kateya-luo/luoye/firmware/docs/UI154_23_CHAPTER_SUMMARY_PREVIEW.png

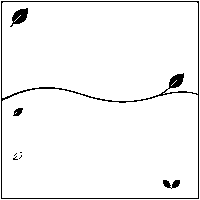
firmware/docs/UI154_23_CHAPTER_SUMMARY_PREVIEW.png
