kateya-luo/luoye/firmware/docs/UI154_23_CHAPTER_SUMMARY_TEXT_PREVIEW.png

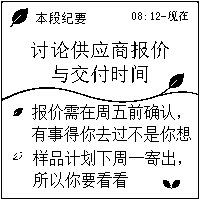
firmware/docs/UI154_23_CHAPTER_SUMMARY_TEXT_PREVIEW.png
