kateya-luo/luoye/firmware/docs/UI154_23PAGES_BW_FAST_PREVIEW.png

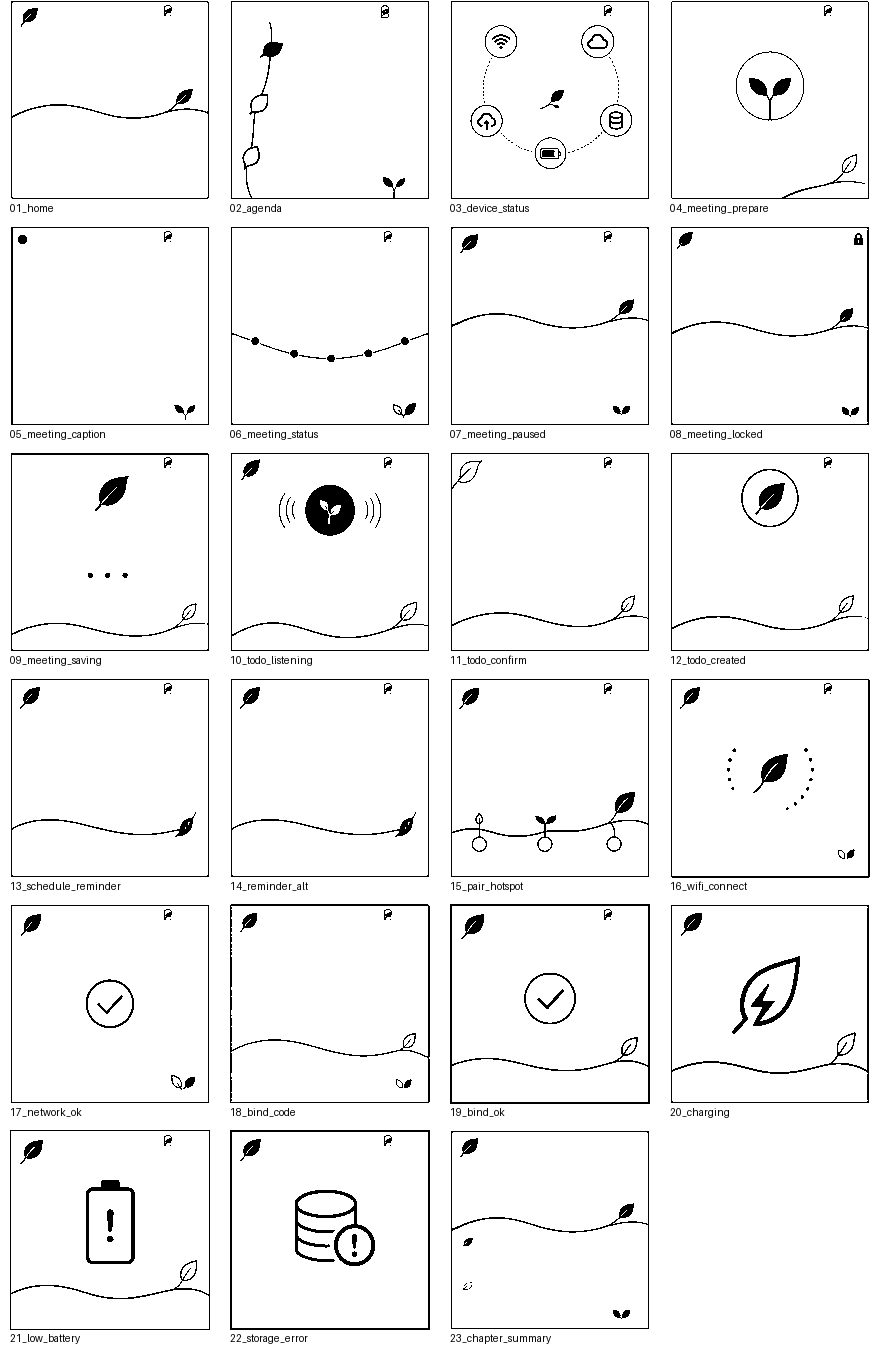
firmware/docs/UI154_23PAGES_BW_FAST_PREVIEW.png
