kateya-luo/luoye/firmware/docs/UI154_FIRMWARE_LIGHT96_FONT_PREVIEW.png

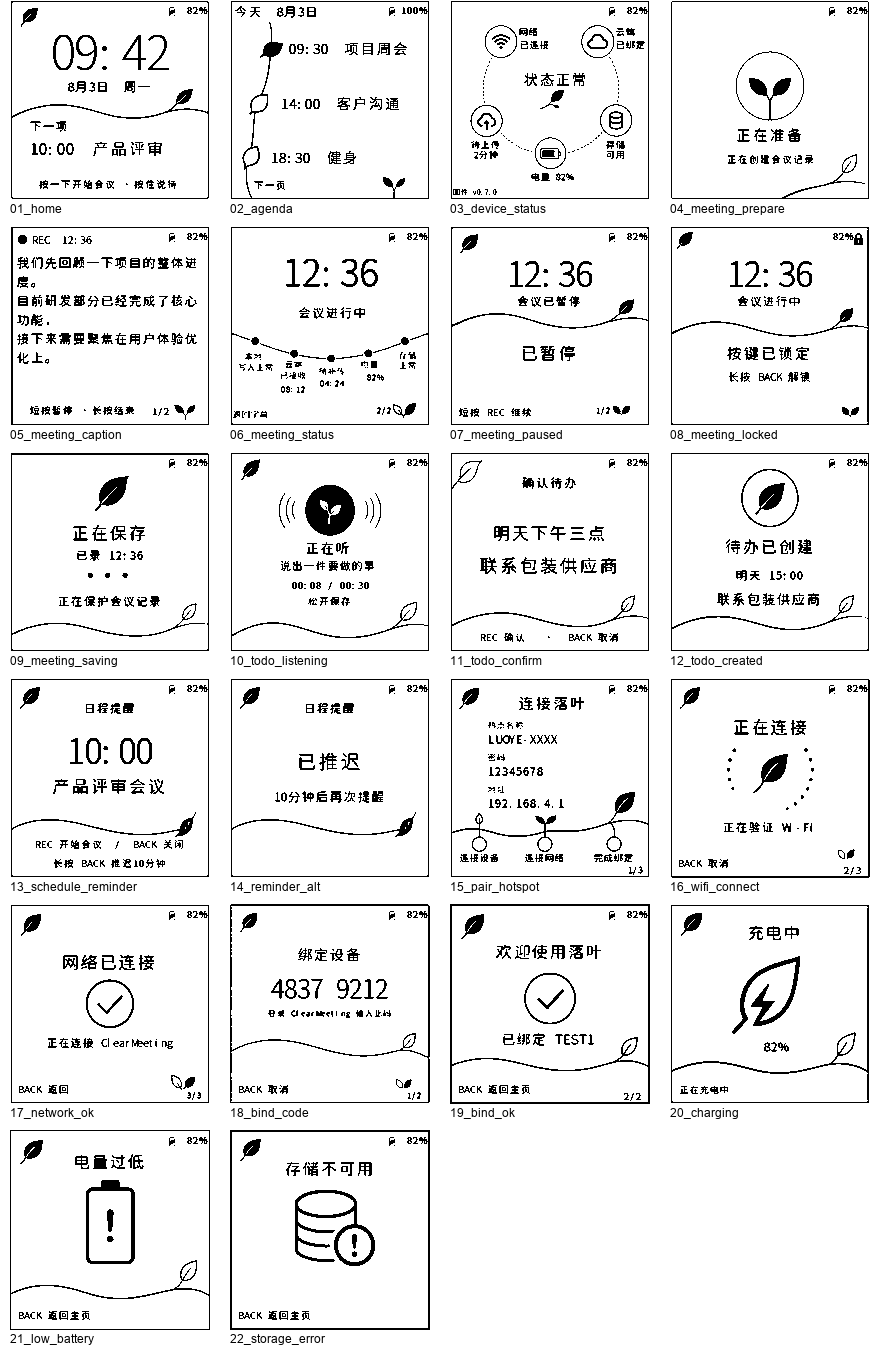
firmware/docs/UI154_FIRMWARE_LIGHT96_FONT_PREVIEW.png
