kateya-luo/luoye/firmware/docs/ui154_firmware_r2_pages/01_home.png

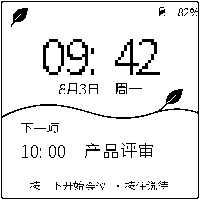
firmware/docs/ui154_firmware_r2_pages/01_home.png
