kateya-luo/luoye/firmware/docs/ui154_firmware_r2_pages/03_device_status.png

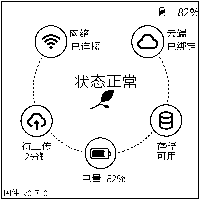
firmware/docs/ui154_firmware_r2_pages/03_device_status.png
