kateya-luo/luoye/firmware/docs/ui154_firmware_r2_pages/04_meeting_prepare.png

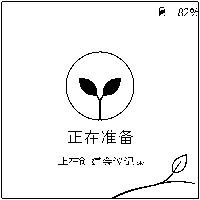
firmware/docs/ui154_firmware_r2_pages/04_meeting_prepare.png
