kateya-luo/luoye/firmware/docs/ui154_firmware_r2_pages/05_meeting_caption.png

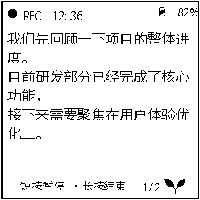
firmware/docs/ui154_firmware_r2_pages/05_meeting_caption.png
