kateya-luo/luoye/firmware/docs/ui154_firmware_r2_pages/06_meeting_status.png

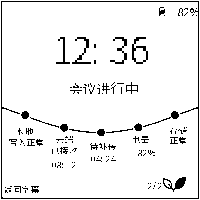
firmware/docs/ui154_firmware_r2_pages/06_meeting_status.png
