kateya-luo/luoye/firmware/docs/ui154_firmware_r2_pages/07_meeting_paused.png

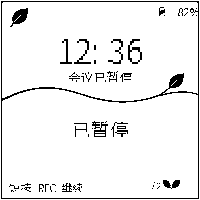
firmware/docs/ui154_firmware_r2_pages/07_meeting_paused.png
