kateya-luo/luoye/firmware/docs/ui154_firmware_r2_pages/08_meeting_locked.png

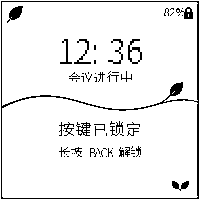
firmware/docs/ui154_firmware_r2_pages/08_meeting_locked.png
