kateya-luo/luoye/firmware/docs/ui154_firmware_r2_pages/09_meeting_saving.png

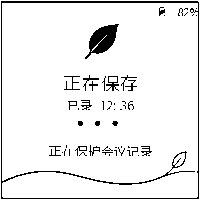
firmware/docs/ui154_firmware_r2_pages/09_meeting_saving.png
