kateya-luo/luoye/firmware/docs/ui154_firmware_r2_pages/13_schedule_reminder.png

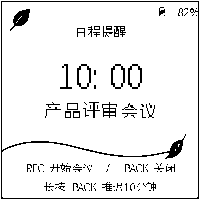
firmware/docs/ui154_firmware_r2_pages/13_schedule_reminder.png
