kateya-luo/luoye/firmware/docs/ui154_firmware_r2_pages/14_reminder_alt.png

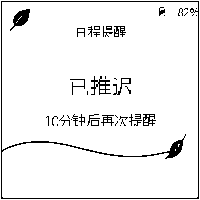
firmware/docs/ui154_firmware_r2_pages/14_reminder_alt.png
