kateya-luo/luoye/firmware/docs/ui154_firmware_r2_pages/15_pair_hotspot.png

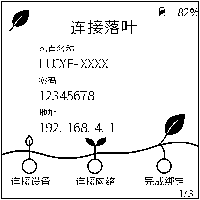
firmware/docs/ui154_firmware_r2_pages/15_pair_hotspot.png
