kateya-luo/luoye/firmware/docs/ui154_firmware_r2_pages/16_wifi_connect.png

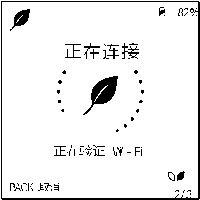
firmware/docs/ui154_firmware_r2_pages/16_wifi_connect.png
