kateya-luo/luoye/firmware/docs/ui154_firmware_r2_pages/17_network_ok.png

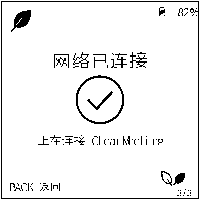
firmware/docs/ui154_firmware_r2_pages/17_network_ok.png
