kateya-luo/luoye/firmware/docs/ui154_firmware_r2_pages/20_charging.png

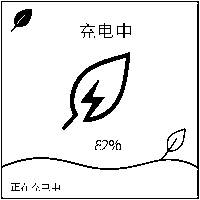
firmware/docs/ui154_firmware_r2_pages/20_charging.png
