kateya-luo/luoye/firmware/docs/ui154_firmware_r2_pages/21_low_battery.png

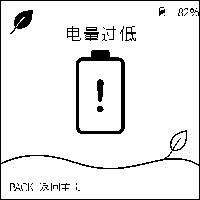
firmware/docs/ui154_firmware_r2_pages/21_low_battery.png
