kateya-luo/luoye/firmware/docs/ui154_firmware_r2_pages/22_storage_error.png

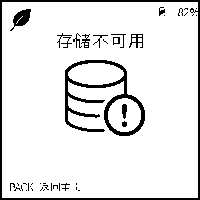
firmware/docs/ui154_firmware_r2_pages/22_storage_error.png
