kateya-luo/luoye/firmware/docs/UI154_FIRMWARE_R2_PREVIEW.png

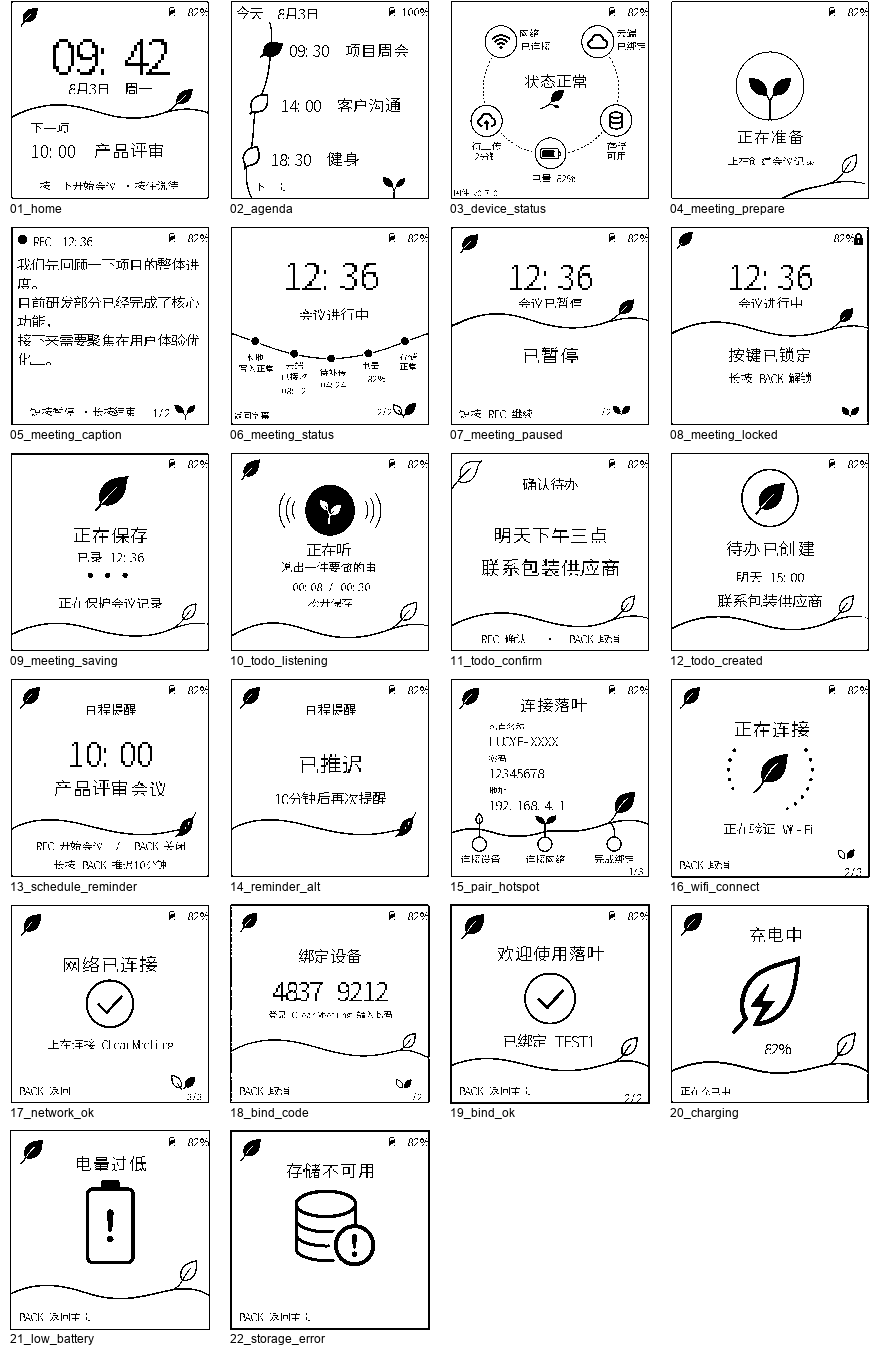
firmware/docs/UI154_FIRMWARE_R2_PREVIEW.png
