kateya-luo/luoye/firmware/docs/UI154_FIRMWARE_REGULAR_NATIVE_PREVIEW.png

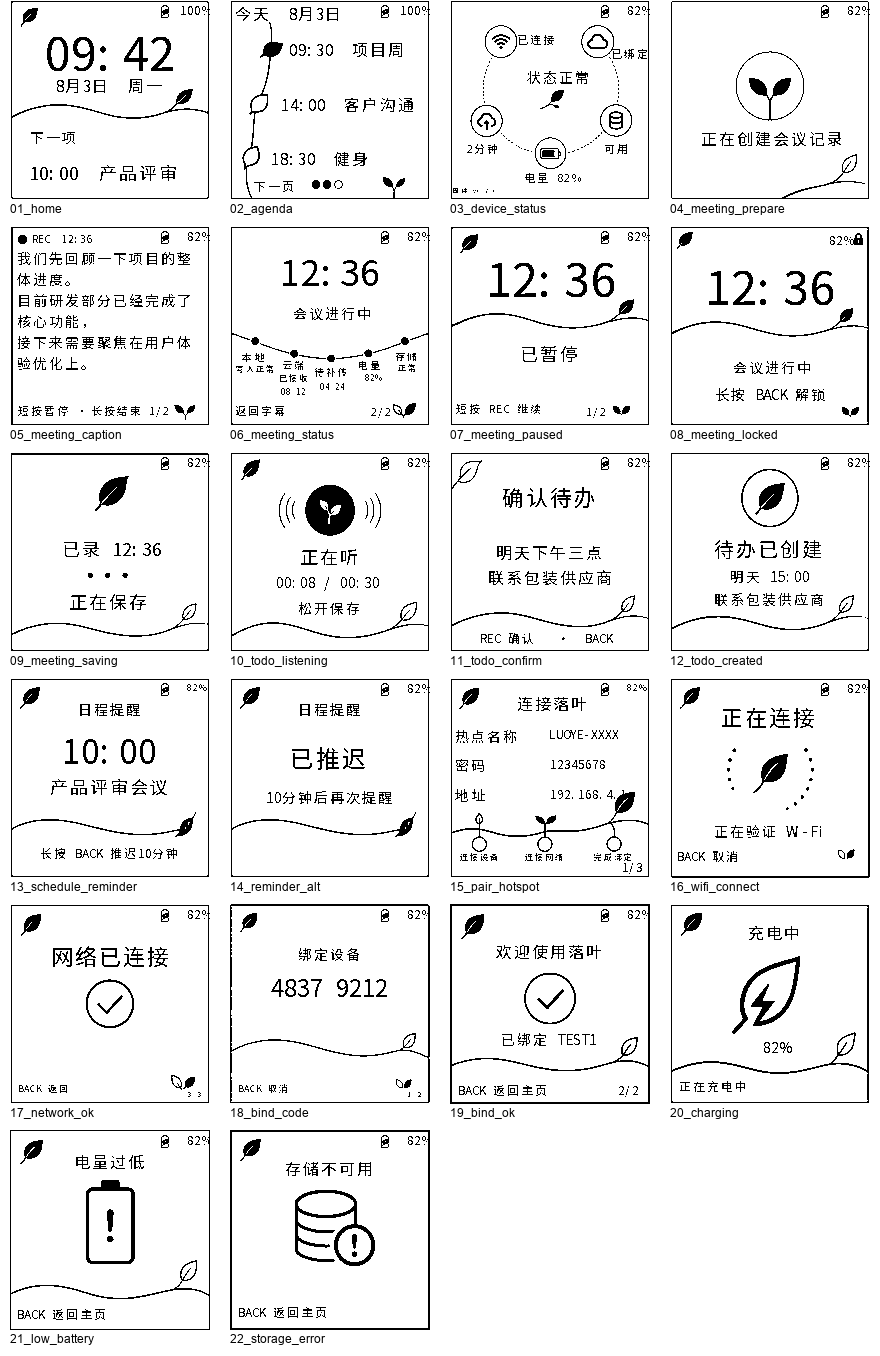
firmware/docs/UI154_FIRMWARE_REGULAR_NATIVE_PREVIEW.png
