kateya-luo/luoye/firmware/docs/UI154_FIRMWARE_SIMSUN_BW_FAST_PREVIEW.png

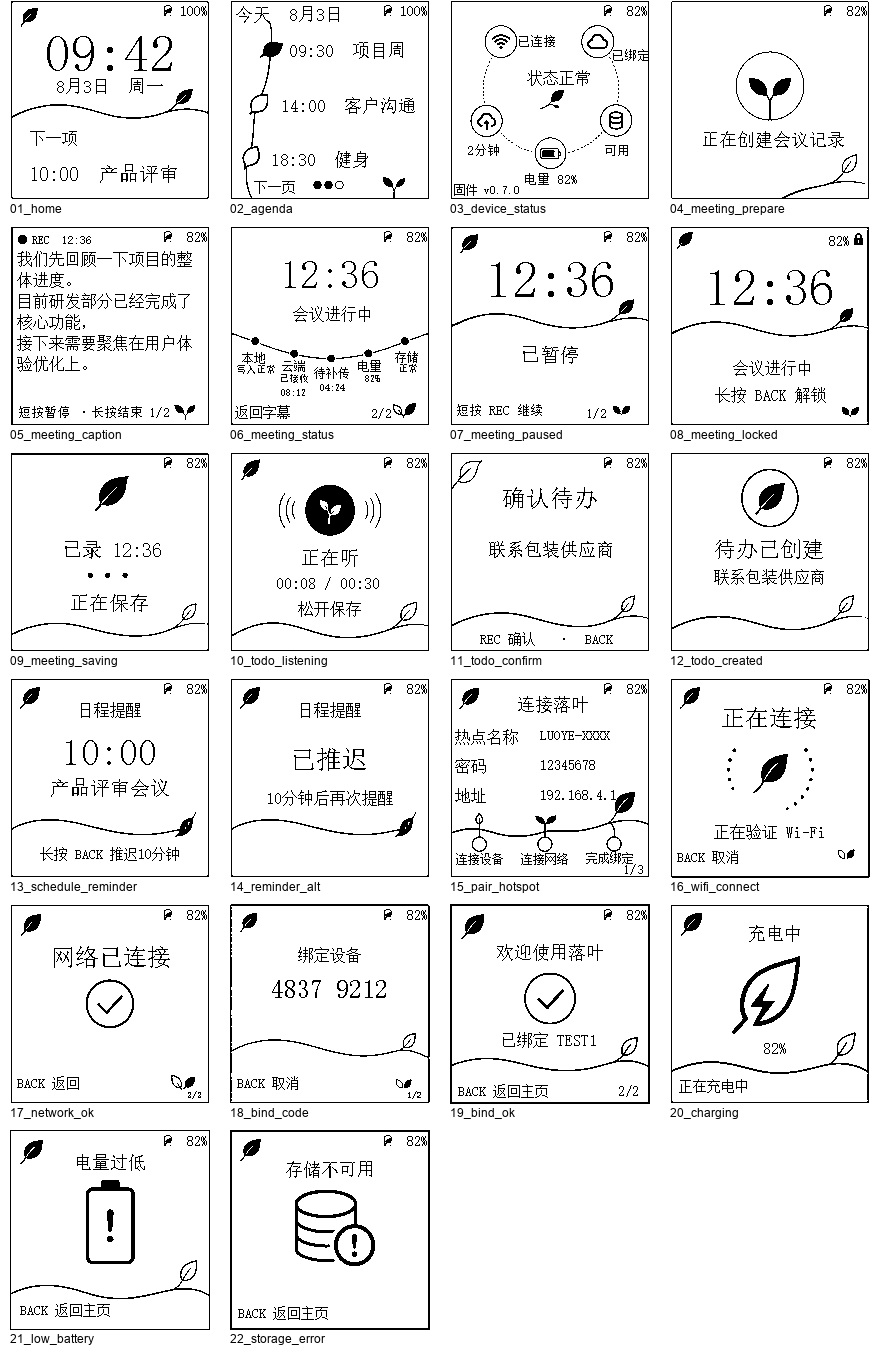
firmware/docs/UI154_FIRMWARE_SIMSUN_BW_FAST_PREVIEW.png
