kateya-luo/luoye/firmware/docs/UI154_FIRMWARE_SIMSUN_GRAY4_PREVIEW.png

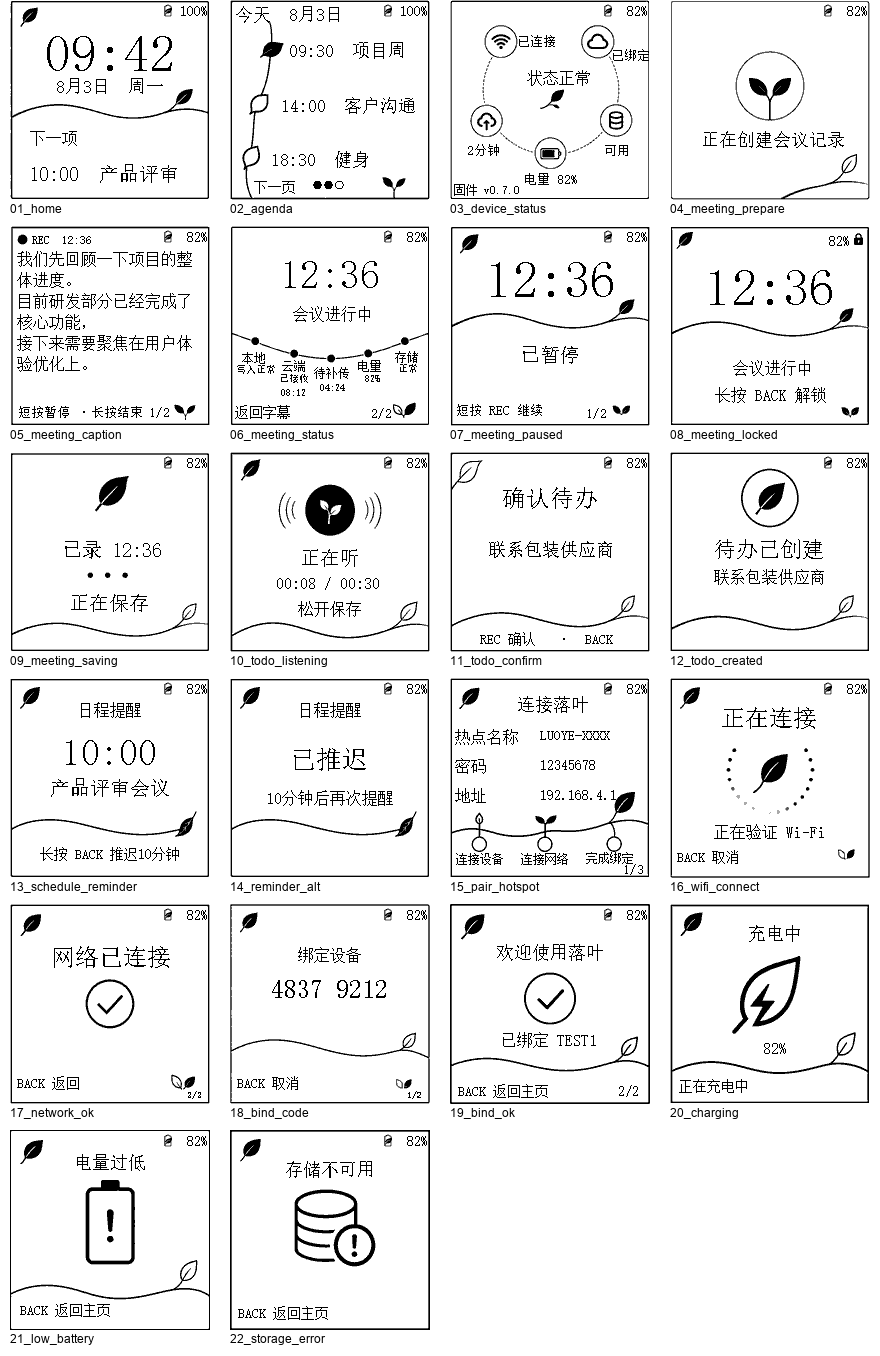
firmware/docs/UI154_FIRMWARE_SIMSUN_GRAY4_PREVIEW.png
