kateya-luo/luoye/firmware/docs/ui154_native_font_pages/01_home.png

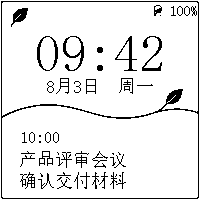
firmware/docs/ui154_native_font_pages/01_home.png
