kateya-luo/luoye/firmware/docs/ui154_native_font_pages/02_agenda.png

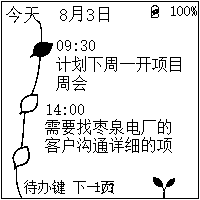
firmware/docs/ui154_native_font_pages/02_agenda.png
