kateya-luo/luoye/firmware/docs/ui154_native_font_pages/04_meeting_prepare.png

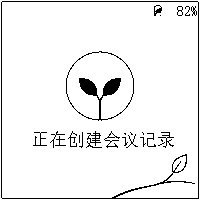
firmware/docs/ui154_native_font_pages/04_meeting_prepare.png
