kateya-luo/luoye/firmware/docs/ui154_native_font_pages/05_meeting_caption.png

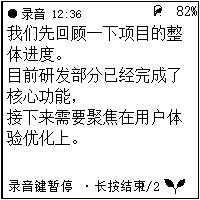
firmware/docs/ui154_native_font_pages/05_meeting_caption.png
