kateya-luo/luoye/firmware/docs/ui154_native_font_pages/07_meeting_paused.png

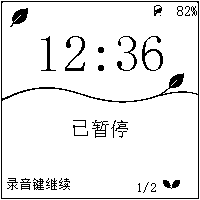
firmware/docs/ui154_native_font_pages/07_meeting_paused.png
