kateya-luo/luoye/firmware/docs/ui154_native_font_pages/08_meeting_locked.png

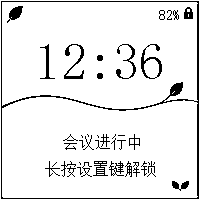
firmware/docs/ui154_native_font_pages/08_meeting_locked.png
