kateya-luo/luoye/firmware/docs/ui154_native_font_pages/09_meeting_saving.png

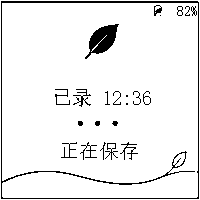
firmware/docs/ui154_native_font_pages/09_meeting_saving.png
