kateya-luo/luoye/firmware/docs/ui154_native_font_pages/13_schedule_reminder.png

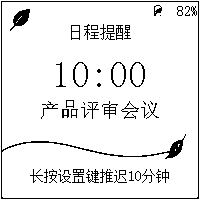
firmware/docs/ui154_native_font_pages/13_schedule_reminder.png
