kateya-luo/luoye/firmware/docs/ui154_native_font_pages/14_reminder_alt.png

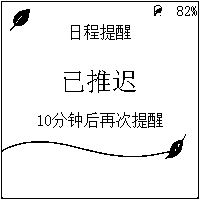
firmware/docs/ui154_native_font_pages/14_reminder_alt.png
