kateya-luo/luoye/firmware/docs/ui154_native_font_pages/15_pair_hotspot.png

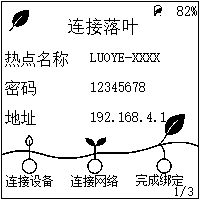
firmware/docs/ui154_native_font_pages/15_pair_hotspot.png
