kateya-luo/luoye/firmware/docs/ui154_native_font_pages/16_wifi_connect.png

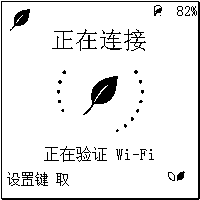
firmware/docs/ui154_native_font_pages/16_wifi_connect.png
