kateya-luo/luoye/firmware/docs/ui154_native_font_pages/18_bind_code.png

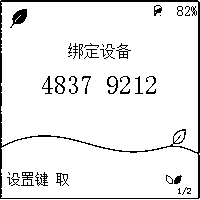
firmware/docs/ui154_native_font_pages/18_bind_code.png
