kateya-luo/luoye/firmware/docs/ui154_native_font_pages/19_bind_ok.png

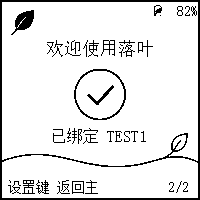
firmware/docs/ui154_native_font_pages/19_bind_ok.png
