kateya-luo/luoye/firmware/docs/ui154_native_font_pages/20_charging.png

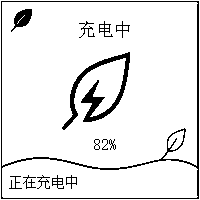
firmware/docs/ui154_native_font_pages/20_charging.png
