kateya-luo/luoye/firmware/docs/ui154_native_font_pages/21_low_battery.png

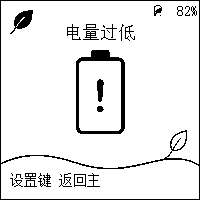
firmware/docs/ui154_native_font_pages/21_low_battery.png
