kateya-luo/luoye/firmware/docs/ui154_native_font_pages/22_storage_error.png

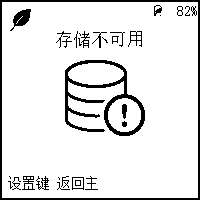
firmware/docs/ui154_native_font_pages/22_storage_error.png
