kateya-luo/luoye/firmware/docs/UI154_THRESHOLD_112.png

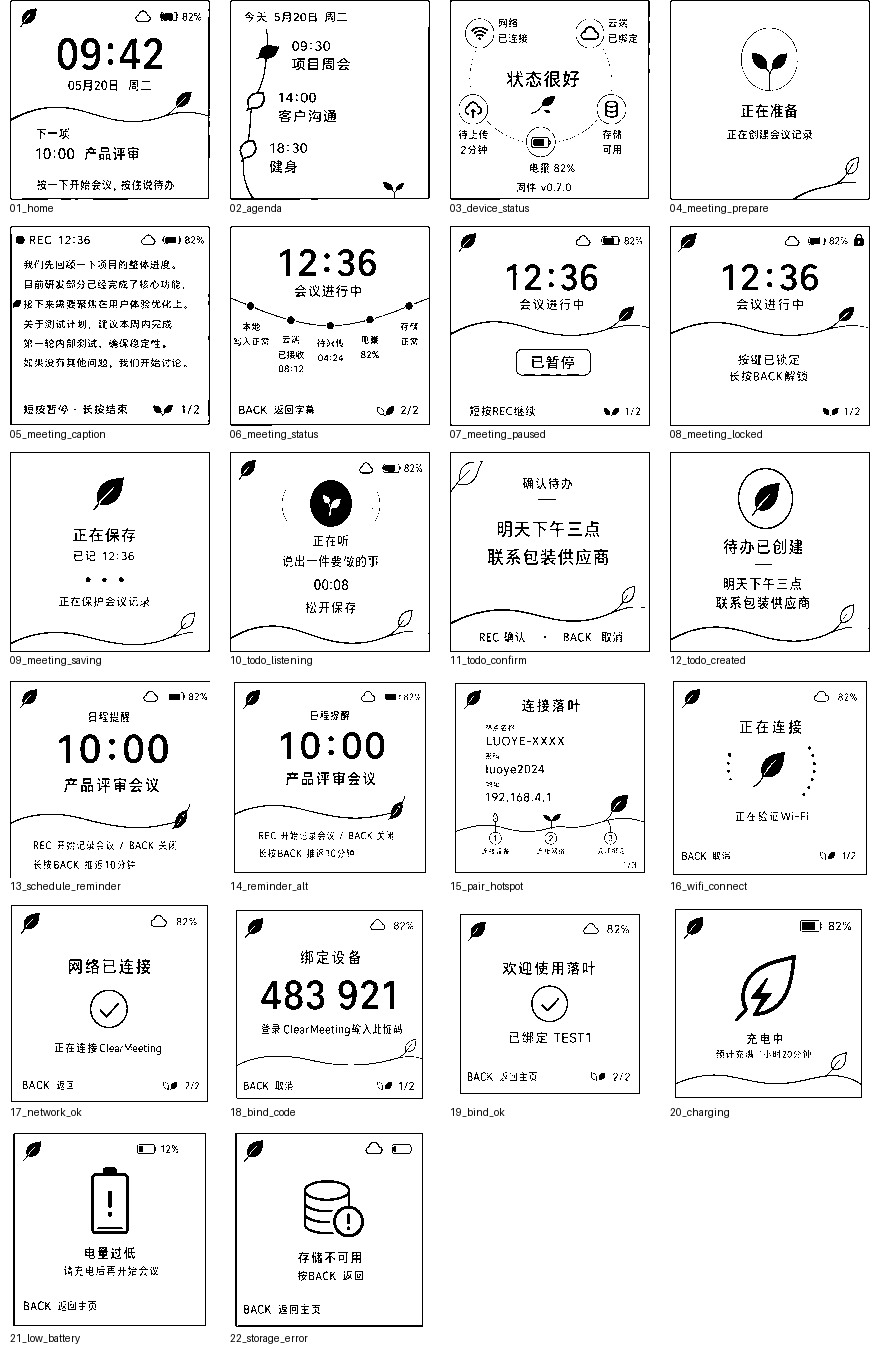
firmware/docs/UI154_THRESHOLD_112.png
