kateya-luo/luoye/firmware/docs/UI154_THRESHOLD_192.png

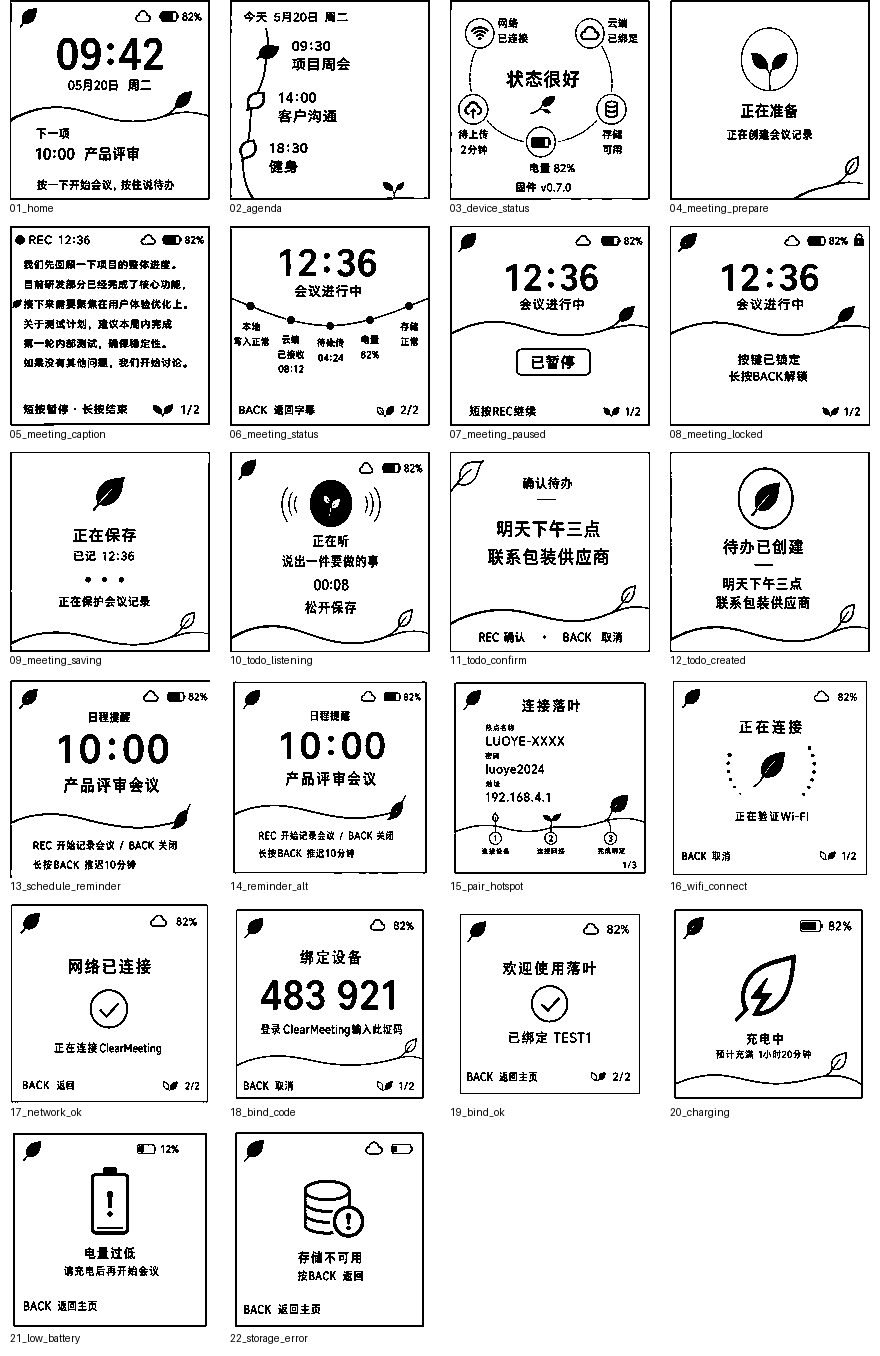
firmware/docs/UI154_THRESHOLD_192.png
