kateya-luo/luoye/firmware/docs/ui154_firmware_r2_pages/10_todo_listening.png

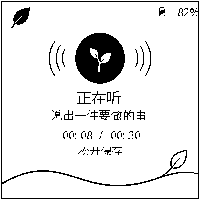
firmware/docs/ui154_firmware_r2_pages/10_todo_listening.png
