kateya-luo/luoye/firmware/docs/ui154_firmware_r2_pages/11_todo_confirm.png

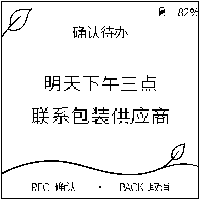
firmware/docs/ui154_firmware_r2_pages/11_todo_confirm.png
