kateya-luo/luoye/firmware/docs/ui154_firmware_r2_pages/12_todo_created.png

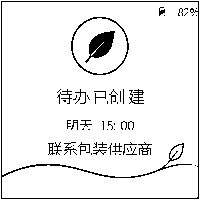
firmware/docs/ui154_firmware_r2_pages/12_todo_created.png
