kateya-luo/luoye/firmware/docs/ui154_native_font_pages/11_todo_confirm.png

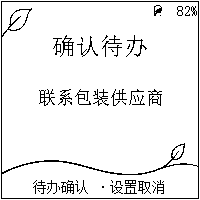
firmware/docs/ui154_native_font_pages/11_todo_confirm.png
