kateya-luo/luoye/firmware/docs/ui154_native_font_pages/12_todo_created.png

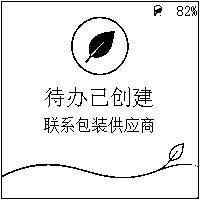
firmware/docs/ui154_native_font_pages/12_todo_created.png
