kateya-luo/luoye/firmware/main/ui_render.c

// Luoye 1.54-inch UI renderer: approved 200x200 artwork + live data overlays.
#include "ui_render.h"
#include "ui_font.h"
#include "luoye_build_info.h"
#include "net_uploader.h"
#include "agenda_todo.h"
#include "epd_ssd1681.h"
#include "ui154_layout_generated.h"

#include <stdio.h>
#include <string.h>
#include <time.h>
#include "esp_log.h"
#include "esp_timer.h"
#include "freertos/FreeRTOS.h"
#include "freertos/semphr.h"
#include "freertos/task.h"

#define DEFAULT_UI_TIMEZONE_OFFSET_MINUTES 480
/* SSD1681 can miss a tiny glyph-only auto-diff after panel sleep.  Keep one
   stable, proven-size window for both dynamic home fields instead: battery
   (158,4,40,17) and clock (27,27,147,52). */
#define HOME_CLOCK_BATTERY_X 24
#define HOME_CLOCK_BATTERY_Y 2
#define HOME_CLOCK_BATTERY_WIDTH 174
#define HOME_CLOCK_BATTERY_HEIGHT 78

static const char *TAG = "ui154";
static uint8_t s_fb[EPD_FB_BYTES];              // packed 1bpp: 0=white, 1=black
static SemaphoreHandle_t s_lock;
static TaskHandle_t s_task;
static volatile int s_pending = -1;
static volatile bool s_busy;
static bool s_assets_ready;
static bool s_have_panel_screen;
static uint32_t s_panel_screen;

/* Stable identity of the visual page, intentionally excluding values that can
   change inside the same page (clock, battery, network and upload status).
   This is the final guard against an asynchronous partial request painting a
   different page over the previous panel image. */
static uint32_t screen_identity(const app_state_t *state) {
  if (!state) return 0;
  if (state->overlay != APP_OV_NONE) {
    return 0x10000U | (uint32_t)state->overlay;
  }
  switch (state->mode) {
    case APP_MODE_STANDBY:
      if (state->page == 0 && state->charging != APP_CHG_NONE) return 0x20010U;
      if (state->page == 1) {
        return 0x20020U | ((uint32_t)state->agenda_page << 8);
      }
      if (state->page == 2) return 0x20030U;
      return 0x20000U;
    case APP_MODE_STARTING: return 0x30000U;
    case APP_MODE_RECORDING:
      if (state->locked) return 0x40010U;
      if (state->paused) return 0x40020U;
      if ((state->page & 1U) != 0) return 0x40030U;
      return 0x40000U;
    case APP_MODE_CLOSING: return 0x50000U;
    case APP_MODE_ENDING: return 0x50010U;
    case APP_MODE_STORAGE_ERROR:
      return 0x60000U | (uint32_t)state->error;
    case APP_MODE_PAIRING:
      return 0x70000U | (uint32_t)state->pairing;
    case APP_MODE_OFF: return 0x80000U;
    default: return 0x90000U | (uint32_t)state->mode;
  }
}

static bool home_clock_active(const app_state_t *state) {
  return state && state->mode == APP_MODE_STANDBY &&
         state->overlay == APP_OV_NONE && state->page == 0 &&
         state->charging == APP_CHG_NONE;
}

static int64_t ui_clock_seconds(void) {
  time_t now = time(NULL);
  int64_t monotonic_ms = esp_timer_get_time() / 1000;
  return now >= 1577836800 ? (int64_t)now : monotonic_ms / 1000;
}

// 5x7 ASCII for compact status fields and a usable fallback when font16.bin is absent.
static const uint8_t FONT[59][5] = {
  {0x00,0x00,0x00,0x00,0x00},{0x00,0x00,0x5F,0x00,0x00},{0x00,0x07,0x00,0x07,0x00},
  {0x14,0x7F,0x14,0x7F,0x14},{0x24,0x2A,0x7F,0x2A,0x12},{0x23,0x13,0x08,0x64,0x62},
  {0x36,0x49,0x55,0x22,0x50},{0x00,0x05,0x03,0x00,0x00},{0x00,0x1C,0x22,0x41,0x00},
  {0x00,0x41,0x22,0x1C,0x00},{0x14,0x08,0x3E,0x08,0x14},{0x08,0x08,0x3E,0x08,0x08},
  {0x00,0x50,0x30,0x00,0x00},{0x08,0x08,0x08,0x08,0x08},{0x00,0x60,0x60,0x00,0x00},
  {0x20,0x10,0x08,0x04,0x02},{0x3E,0x51,0x49,0x45,0x3E},{0x00,0x42,0x7F,0x40,0x00},
  {0x42,0x61,0x51,0x49,0x46},{0x21,0x41,0x45,0x4B,0x31},{0x18,0x14,0x12,0x7F,0x10},
  {0x27,0x45,0x45,0x45,0x39},{0x3C,0x4A,0x49,0x49,0x30},{0x01,0x71,0x09,0x05,0x03},
  {0x36,0x49,0x49,0x49,0x36},{0x06,0x49,0x49,0x29,0x1E},{0x00,0x36,0x36,0x00,0x00},
  {0x00,0x56,0x36,0x00,0x00},{0x08,0x14,0x22,0x41,0x00},{0x14,0x14,0x14,0x14,0x14},
  {0x00,0x41,0x22,0x14,0x08},{0x02,0x01,0x51,0x09,0x06},{0x32,0x49,0x79,0x41,0x3E},
  {0x7E,0x11,0x11,0x11,0x7E},{0x7F,0x49,0x49,0x49,0x36},{0x3E,0x41,0x41,0x41,0x22},
  {0x7F,0x41,0x41,0x22,0x1C},{0x7F,0x49,0x49,0x49,0x41},{0x7F,0x09,0x09,0x09,0x01},
  {0x3E,0x41,0x49,0x49,0x7A},{0x7F,0x08,0x08,0x08,0x7F},{0x00,0x41,0x7F,0x41,0x00},
  {0x20,0x40,0x41,0x3F,0x01},{0x7F,0x08,0x14,0x22,0x41},{0x7F,0x40,0x40,0x40,0x40},
  {0x7F,0x02,0x0C,0x02,0x7F},{0x7F,0x04,0x08,0x10,0x7F},{0x3E,0x41,0x41,0x41,0x3E},
  {0x7F,0x09,0x09,0x09,0x06},{0x3E,0x41,0x51,0x21,0x5E},{0x7F,0x09,0x19,0x29,0x46},
  {0x46,0x49,0x49,0x49,0x31},{0x01,0x01,0x7F,0x01,0x01},{0x3F,0x40,0x40,0x40,0x3F},
  {0x1F,0x20,0x40,0x20,0x1F},{0x3F,0x40,0x38,0x40,0x3F},{0x63,0x14,0x08,0x14,0x63},
  {0x07,0x08,0x70,0x08,0x07},{0x61,0x51,0x49,0x45,0x43},
};

void ui_fb_rect(int x, int y, int w, int h) {
  for (int py = y; py < y + h; py++) {
    if (py < 0 || py >= EPD_LANDSCAPE_H) continue;
    for (int px = x; px < x + w; px++) {
      if (px < 0 || px >= EPD_LANDSCAPE_W) continue;
      size_t index = py * EPD_FB_STRIDE + (px >> 3);
      s_fb[index] |= (uint8_t)(0x80U >> (px & 7));
    }
  }
}

static void white_rect(int x, int y, int w, int h) {
  for (int py = y; py < y + h; py++) {
    if (py < 0 || py >= EPD_LANDSCAPE_H) continue;
    for (int px = x; px < x + w; px++) {
      if (px < 0 || px >= EPD_LANDSCAPE_W) continue;
      size_t index = py * EPD_FB_STRIDE + (px >> 3);
      s_fb[index] &= (uint8_t)~(0x80U >> (px & 7));
    }
  }
}

static void ascii_char(int x, int y, int scale, char c) {
  if (c >= 'a' && c <= 'z') c -= 32;
  const uint8_t box[5] = {0x7F, 0x41, 0x41, 0x41, 0x7F};
  const uint8_t *glyph = (c >= 32 && c <= 90) ? FONT[c - 32] : box;
  for (int col = 0; col < 5; col++) {
    for (int row = 0; row < 7; row++) {
      if (glyph[col] & (1U << row)) {
        ui_fb_rect(x + col * scale, y + row * scale, scale, scale);
      }
    }
  }
}

static void ascii_text(int x, int y, int scale, const char *text) {
  for (; text && *text; text++, x += 6 * scale) ascii_char(x, y, scale, *text);
}

static int utext(int x, int y, int scale, const char *text) {
  if (ui_font_ready()) return ui_font_text(x, y, scale, text ? text : "");
  ascii_text(x, y + 4 * scale, scale, text ? text : "");
  return x + (int)strlen(text ? text : "") * 6 * scale;
}

static int utext_w(const char *text, int scale) {
  return ui_font_ready() ? ui_font_text_w(text ? text : "", scale)
                         : (int)strlen(text ? text : "") * 6 * scale;
}

static void ucenter(int y, int scale, const char *text) {
  utext((EPD_LANDSCAPE_W - utext_w(text, scale)) / 2, y, scale, text);
}

static const char *next_utf8(const char *text) {
  if (!text || !*text) return text;
  text++;
  while (*text && (((unsigned char)*text & 0xC0U) == 0x80U)) text++;
  return text;
}

static void wrap_text(int x, int y, int max_width, int max_lines,
                      int line_height, const char *text) {
  int cx = x;
  int line = 0;
  char one[8];
  while (text && *text && line < max_lines) {
    const char *next = next_utf8(text);
    size_t length = (size_t)(next - text);
    if (length >= sizeof(one)) break;
    memcpy(one, text, length);
    one[length] = '\0';
    int advance = utext_w(one, 1);
    if (cx + advance > x + max_width) {
      cx = x;
      if (++line >= max_lines) break;
    }
    utext(cx, y + line * line_height, 1, one);
    cx += advance;
    text = next;
  }
}

static bool load_page(const char *page_id) {
  memset(s_fb, 0, sizeof(s_fb));
  if (!s_assets_ready || !page_id) return false;
  char path[80];
  snprintf(path, sizeof(path), "/assets/ui154/%s.bin", page_id);
  FILE *file = fopen(path, "rb");
  if (!file) {
    ESP_LOGW(TAG, "missing UI asset: %s", path);
    return false;
  }
  size_t got = fread(s_fb, 1, sizeof(s_fb), file);
  int extra = fgetc(file);
  fclose(file);
  if (got != sizeof(s_fb) || extra != EOF) {
    ESP_LOGE(TAG, "invalid UI asset size: %s (%u)", path, (unsigned)got);
    memset(s_fb, 0, sizeof(s_fb));
    return false;
  }
  return true;
}

#define UI154_LAYOUT_MAX_LINES 8
#define UI154_LAYOUT_LINE_BYTES 256

typedef struct {
  char text[UI154_LAYOUT_LINE_BYTES];
  int width;
} layout_line_t;

static int layout_char_width(const char *start, size_t length, int pixel_size) {
  char one[8];
  if (!start || length == 0 || length >= sizeof(one)) return 0;
  memcpy(one, start, length);
  one[length] = '\0';
  return ui_font_ready() ? ui_font_text_w_px(one, pixel_size)
                         : (int)length * 6 * ((pixel_size + 6) / 7);
}

static bool layout_text_fits(const ui154_layout_field_t *field, const char *text) {
  int line = 1;
  int width = 0;
  while (text && *text) {
    if (*text == '\n') {
      if (++line > field->max_lines) return false;
      width = 0;
      text++;
      continue;
    }
    const char *next = next_utf8(text);
    int advance = layout_char_width(text, (size_t)(next - text), field->size);
    if (width > 0 && width + advance > field->width) {
      if (++line > field->max_lines) return false;
      width = 0;
    }
    width += advance;
    text = next;
  }
  return true;
}
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
